chaostreff-flensburg/rakede-pcb/img/rakede-sticker-98mm.png

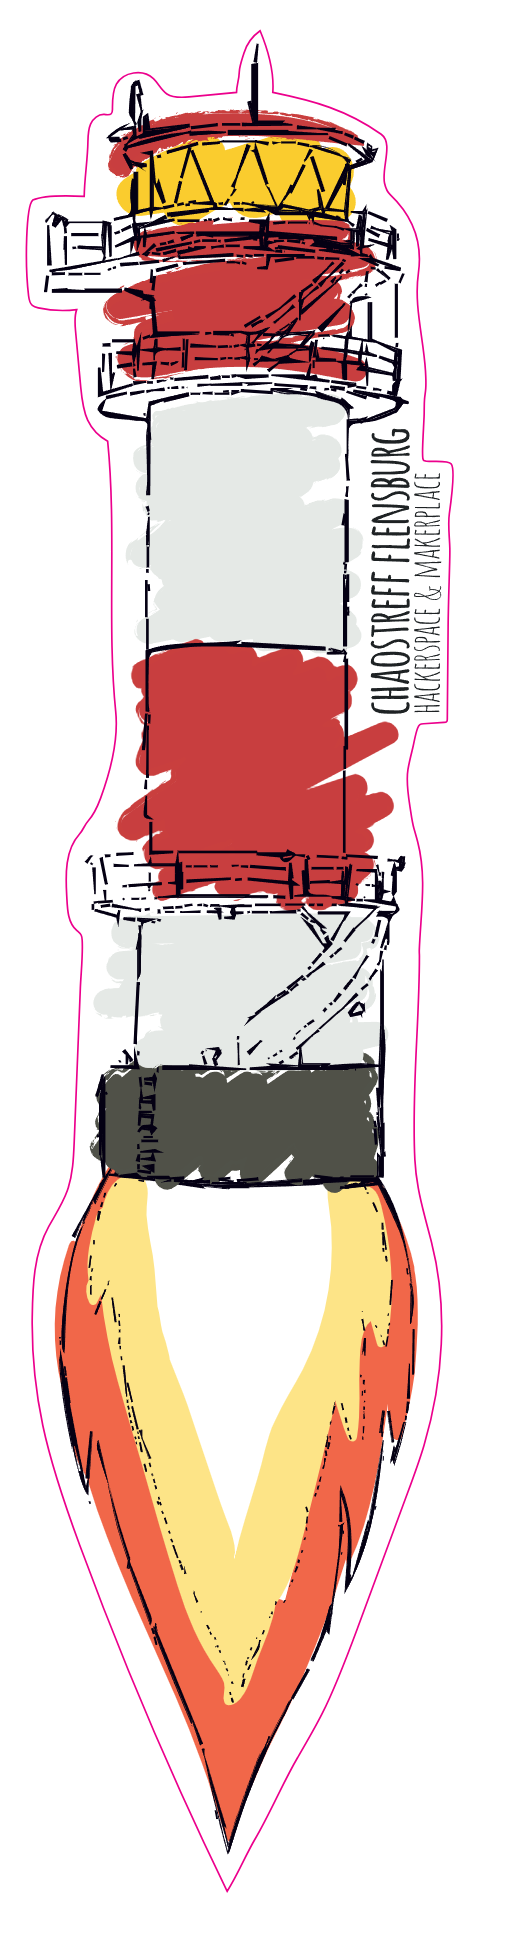
img/rakede-sticker-98mm.png
